Spritetm/esppdp/firmware/main/pdp11_io_lib.c

/* pdp11_io_lib.c: Unibus/Qbus common support routines

   Copyright (c) 1993-2017, Robert M Supnik

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
   Except as contained in this notice, the name of Robert M Supnik shall not be
   used in advertising or otherwise to promote the sale, use or other dealings
   in this Software without prior written authorization from Robert M Supnik.
*/

#if defined (VM_PDP10)                                  /* PDP10 version */
#include "pdp10_defs.h"

#elif defined (VM_VAX)                                  /* VAX version */
#include "vax_defs.h"

#else                                                   /* PDP-11 version */
#include "pdp11_defs.h"
#endif
#include "sim_sock.h"
#include "sim_term.h"
#include "sim_ether.h"

extern int32 int_vec[IPL_HLVL][32];
#if !defined(VEC_SET)
#define VEC_SET 0
#endif
#if (VEC_SET != 0)
extern int32 int_vec_set[IPL_HLVL][32];                 /* bits to set in vector */
#endif
extern int32 (*int_ack[IPL_HLVL][32])(void);
extern DIB *iodibp[IOPAGESIZE >> 1];

extern t_stat build_dib_tab (void);

static void build_vector_tab (void);

#if !defined(UNIMEMSIZE)
#define UNIMEMSIZE      001000000                       /* 2**18 */
#endif

#define AUTO_MAXC       32              /* Maximum number of controllers */
#define AUTO_CSRBASE    0010
#define AUTO_CSRMAX    04000
#define AUTO_VECBASE    0300

/* Enable/disable autoconfiguration */

t_stat set_autocon (UNIT *uptr, int32 val, CONST char *cptr, void *desc)
{
if (cptr != NULL)
    return SCPE_ARG;
if (autcon_enb == val)
    return SCPE_OK;
autcon_enb = val;
if (autcon_enb == 0) {
    sim_messagef (SCPE_OK, "Device auto configuration is now disabled.\n");
    sim_messagef (SCPE_OK, "Explicitly setting any address or vector value tells the system\n");
    sim_messagef (SCPE_OK, "that you are planning a specific configuration that may not use\n");
    sim_messagef (SCPE_OK, "use standard values.  You must explicitly specify bus address and\n");
    sim_messagef (SCPE_OK, "vector values for any device you enable or otherwise add to the\n");
    sim_messagef (SCPE_OK, "system configuration after this message is issued.  Changing the\n");
    sim_messagef (SCPE_OK, "number of lines on a terminal multiplexer is such a change.\n");
    sim_messagef (SCPE_OK, "To avoid complexities dealing with this, it is recommended that\n");
    sim_messagef (SCPE_OK, "you configure all devices which can use standard addresses before\n");
    sim_messagef (SCPE_OK, "changing the address or vector for an unusual device situation.\n");
    }
return auto_config (NULL, 0);
}

/* Show autoconfiguration status */

t_stat show_autocon (FILE *st, UNIT *uptr, int32 val, CONST void *desc)
{
fprintf (st, "autoconfiguration ");
fprintf (st, autcon_enb? "enabled": "disabled");
return SCPE_OK;
}

/* Change device address */

t_stat set_addr (UNIT *uptr, int32 val, CONST char *cptr, void *desc)
{
DEVICE *dptr;
DIB *dibp;
uint32 newba;
t_stat r;

if (cptr == NULL)
    return SCPE_ARG;
if ((val == 0) || (uptr == NULL))
    return SCPE_IERR;
dptr = find_dev_from_unit (uptr);
if (dptr == NULL)
    return SCPE_IERR;
dibp = (DIB *) dptr->ctxt;
if (dibp == NULL)
    return SCPE_IERR;
newba = (uint32) get_uint (cptr, DEV_RDX, IOPAGEBASE+IOPAGEMASK, &r); /* get new */
if (r != SCPE_OK)
    return r;
if ((newba <= IOPAGEBASE) ||                            /* > IO page base? */
    (newba % ((uint32) val)))                           /* check modulus */
    return SCPE_ARG;
dibp->ba = newba;                                       /* store */
set_autocon (NULL, 0, NULL, NULL);                      /* autoconfig off */
return SCPE_OK;
}

/* Show device address */

t_stat show_addr (FILE *st, UNIT *uptr, int32 val, CONST void *desc)
{
DEVICE *dptr;
DIB *dibp;
uint32 radix = DEV_RDX;

if (uptr == NULL)
    return SCPE_IERR;
dptr = find_dev_from_unit (uptr);
if (dptr == NULL)
    return SCPE_IERR;
dibp = (DIB *) dptr->ctxt;
if ((dibp == NULL) || (dibp->ba <= IOPAGEBASE))
    return SCPE_IERR;
if ((sim_switches & SWMASK('H')) || (sim_switch_number == 16))
    radix = 16;
if ((sim_switches & SWMASK('O')) || (sim_switch_number == 8))
    radix = 8;
fprintf (st, "address=");
fprint_val (st, (t_value) dibp->ba, DEV_RDX, 32, PV_LEFT);
if (radix != DEV_RDX) {
    fprintf (st, "(");
    fprint_val (st, (t_value) dibp->ba, radix, 32, PV_LEFT);
    fprintf (st, ")");
    }
if (dibp->lnt > 1) {
    fprintf (st, "-");
    fprint_val (st, (t_value) dibp->ba + dibp->lnt - 1, DEV_RDX, 32, PV_LEFT);
    if (radix != DEV_RDX) {
        fprintf (st, "(");
        fprint_val (st, (t_value) dibp->ba + dibp->lnt - 1, radix, 32, PV_LEFT);
        fprintf (st, ")");
        }
    }
if (dibp->ba < IOPAGEBASE + AUTO_CSRBASE + AUTO_CSRMAX)
    fprintf (st, "*");
return SCPE_OK;
}

/* Set address floating */

t_stat set_addr_flt (UNIT *uptr, int32 val, CONST char *cptr, void *desc)
{
DEVICE *dptr;

if (cptr != NULL)
    return SCPE_ARG;
if (uptr == NULL)
    return SCPE_IERR;
dptr = find_dev_from_unit (uptr);
if (dptr == NULL)
    return SCPE_IERR;
return auto_config (NULL, 0);                           /* autoconfigure */
}

/* Show device address */

t_stat show_mapped_addr (FILE *st, UNIT *uptr, int32 val, CONST void *desc)
{
fprintf (st, "address=%p-%p", desc, ((const char *)desc) + uptr->capac - 1);
return SCPE_OK;
}

/* Change device vector */

t_stat set_vec (UNIT *uptr, int32 arg, CONST char *cptr, void *desc)
{
DEVICE *dptr;
DIB *dibp;
uint32 newvec;
t_stat r;

if (cptr == NULL)
    return SCPE_ARG;
if (uptr == NULL)
    return SCPE_IERR;
dptr = find_dev_from_unit (uptr);
if (dptr == NULL)
    return SCPE_IERR;
dibp = (DIB *) dptr->ctxt;
if (dibp == NULL)
    return SCPE_IERR;
newvec = (uint32) get_uint (cptr, DEV_RDX, 01000, &r);
if ((r != SCPE_OK) ||
    ((newvec + (dibp->vnum * 4)) >= 01000) ||           /* total too big? */
    (newvec & ((dibp->vnum > 1)? 07: 03)))              /* properly aligned value? */
    return SCPE_ARG;
dibp->vec = newvec;
set_autocon (NULL, 0, NULL, NULL);                      /* autoconfig off */
return SCPE_OK;
}

/* Show device vector */

t_stat show_vec (FILE *st, UNIT *uptr, int32 arg, CONST void *desc)
{
DEVICE *dptr;
DIB *dibp;
uint32 vec, numvec, br_lvl, radix = DEV_RDX;
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
